juliuszint/wiredSEK/resources/IMG_3607.png

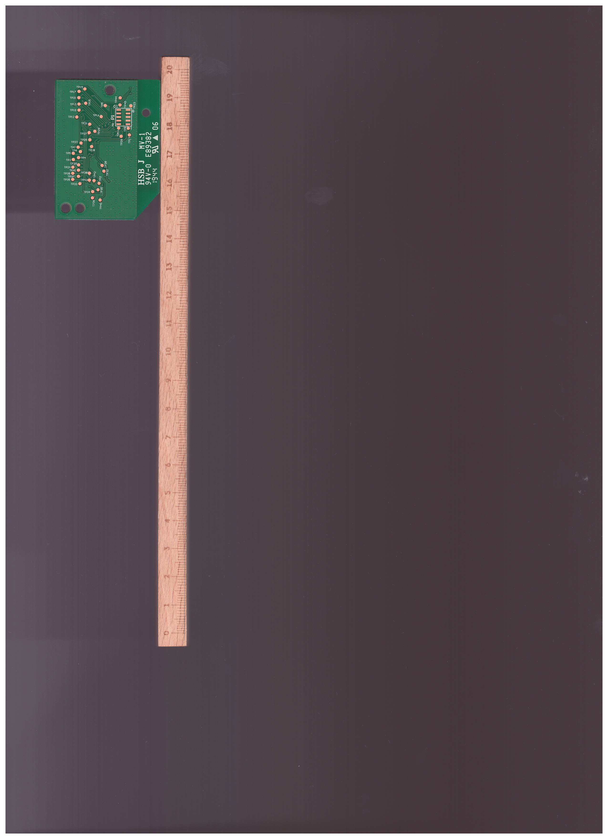
resources/IMG_3607.png
