juliuszint/wiredSEK/resources/IMG_3614_PREVIEW.jpg

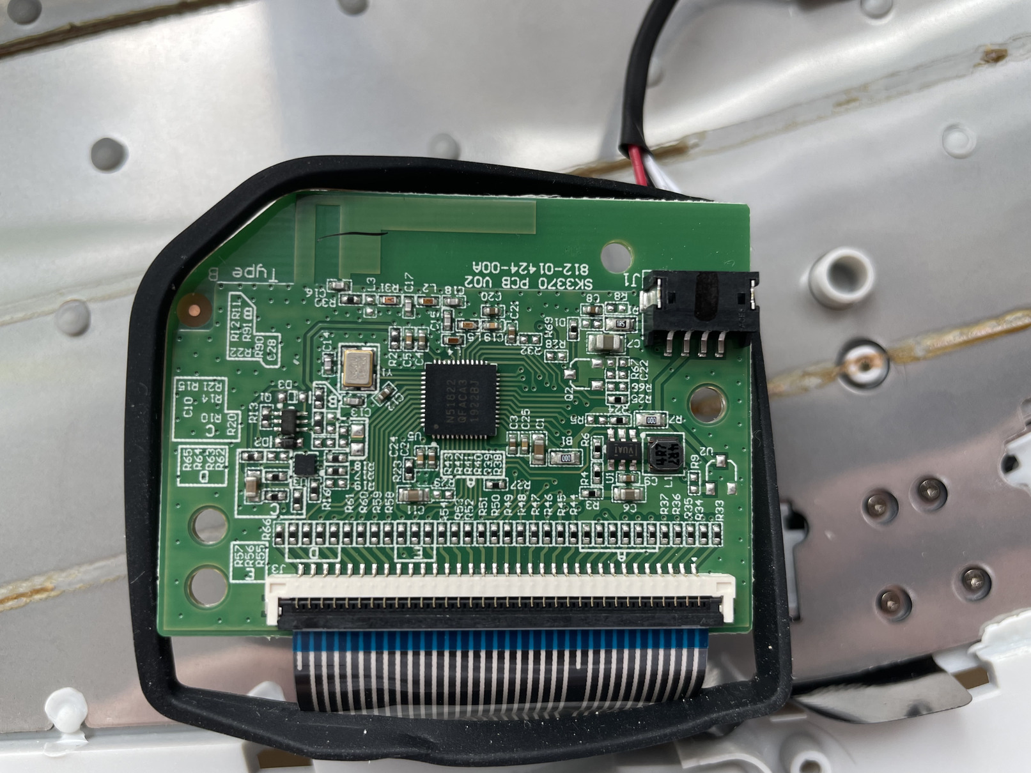
resources/IMG_3614_PREVIEW.jpg
