juliuszint/wiredSEK/resources/IMG_3975.jpg

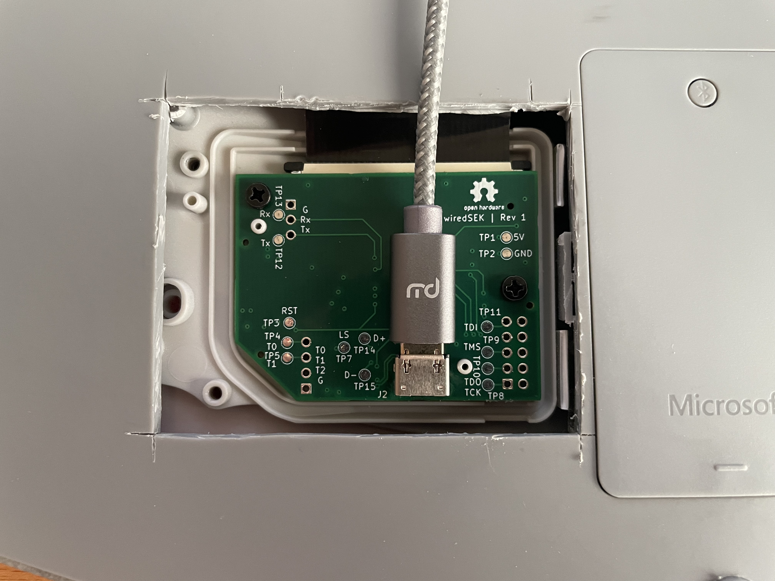
resources/IMG_3975.jpg
